fedeboco/current-feedback-amplifier/spice/sim.asc

C1: cap; 1µ
C2: cap; 1µ
C3: cap; 10p
C4: cap; 10p
C5: cap; 100µ
C6: cap; 47µ
C7: cap; 47µ
D1: zener; D1N5250
D2: zener; D1N5250
D3: diode; DI_1N5408
D4: diode; DI_1N5408
D5: zener; 1N750
Q1: pnp; BC857B
Q2: npn; BC847B
Q3: npn; BC847B
Q4: pnp; BC857B
Q5: npn; BD139
Q6: pnp; QD45VH10
Q7: npn; QD44VH10
Q8: pnp; BD140
Q9: pnp; BC807P
Q10: npn; BC817-16
Q11: pnp; BC807P
Q12: npn; BC817-16
Q13: pnp; BC556B
Q14: npn; BC546B
Q15: npn; BC546B
Q16: npn; BC546B
Q17: pnp; BC556B
Q18: npn; BC847B
Q19: pnp; BC857B
Q20: npn; BC817-16
Q21: pnp; BC807P
Q22: pnp; BC556B
Q23: npn; BC546B
R1: res; 0.22
R2: res; 0.22
R3: res; 680
R4: res; 1k
R5: res; 680
R6: res; 680
R7: res; 8
R8: res; 22k
R9: res; 220
R10: res; 1k
R11: res; 220
R12: res; 10k
R13: res; 22
R14: res; 22k
R15: res; 560
R16: res; 220
R17: res; 10k
R18: res; 100k
R19: res; 3k3
R20: res; 100k
R21: res; 10k
R22: res; 560
R23: res; 680
R24: res; 1k
R25: res; 1k
R26: res; 1k
R27: res; 1k
R28: res; 22
R29: res; 22
R30: res; 22
R31: res; 3.3k
R33: res; 330
R34: res; 100k
R35: res; 1
R36: res; 100
R37: res; 100
RPOTE: res; 85
U1: OP27
U2: OP27
U3: LT1017
V1: voltage; 32
V2: voltage; 32
V3: voltage; PULSE(-1.4 1.4 0 1p 1p 0.5m 1m)
V5: voltage; SINE(0 0 7k)
V6: voltage; ""; AC 1
V7: voltage; 5
V8: voltage; 4.6
Vin: voltage; SINE(0 0 100)
Named nets: 0, Vcc, Vss, Vout, ip, 20V, -20V, 5v, 20v, acin
.tran 0 3m 0.5m 5u
SERVO DC
FEEDBACK
SLEW RATE
.FOUR 1kHz 20 V(Vout)
;noise V(Vout) Vin dec 100 10 200k
;ac dec 100 0.001 100e6
RTA FREC
ALIM. OPERACIONAL
50ms MCM (IMD)
