fedeboco/current-feedback-amplifier/schematic/REFERENCIAS ARMADO/VISTAFRONTALV3.13.jpg

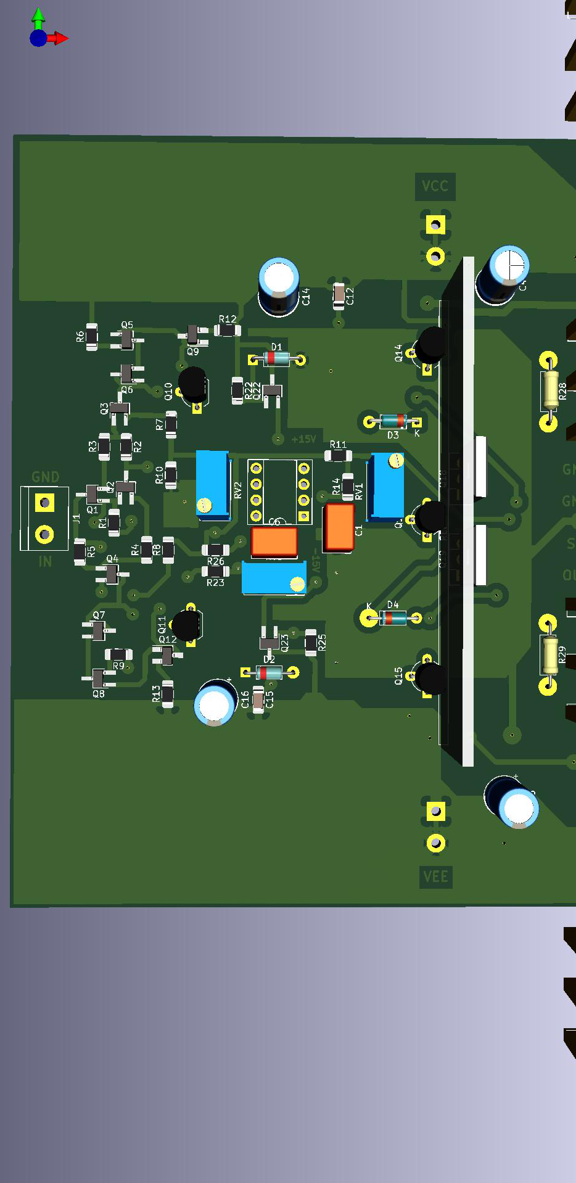
schematic/REFERENCIAS ARMADO/VISTAFRONTALV3.13.jpg
