fedeboco/current-feedback-amplifier/schematic/REFERENCIAS ARMADO/VISTATRASERAV3.13.jpg

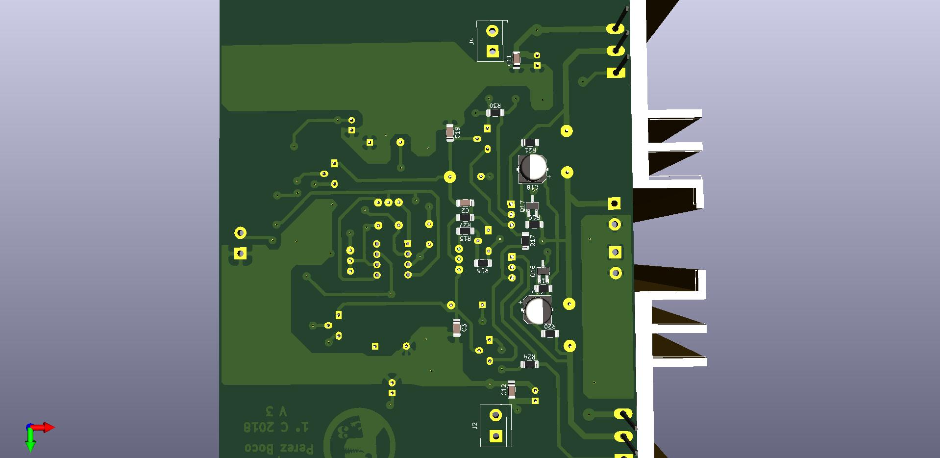
schematic/REFERENCIAS ARMADO/VISTATRASERAV3.13.jpg
